cyril279/keyboards/documentation/pg1353.jpg

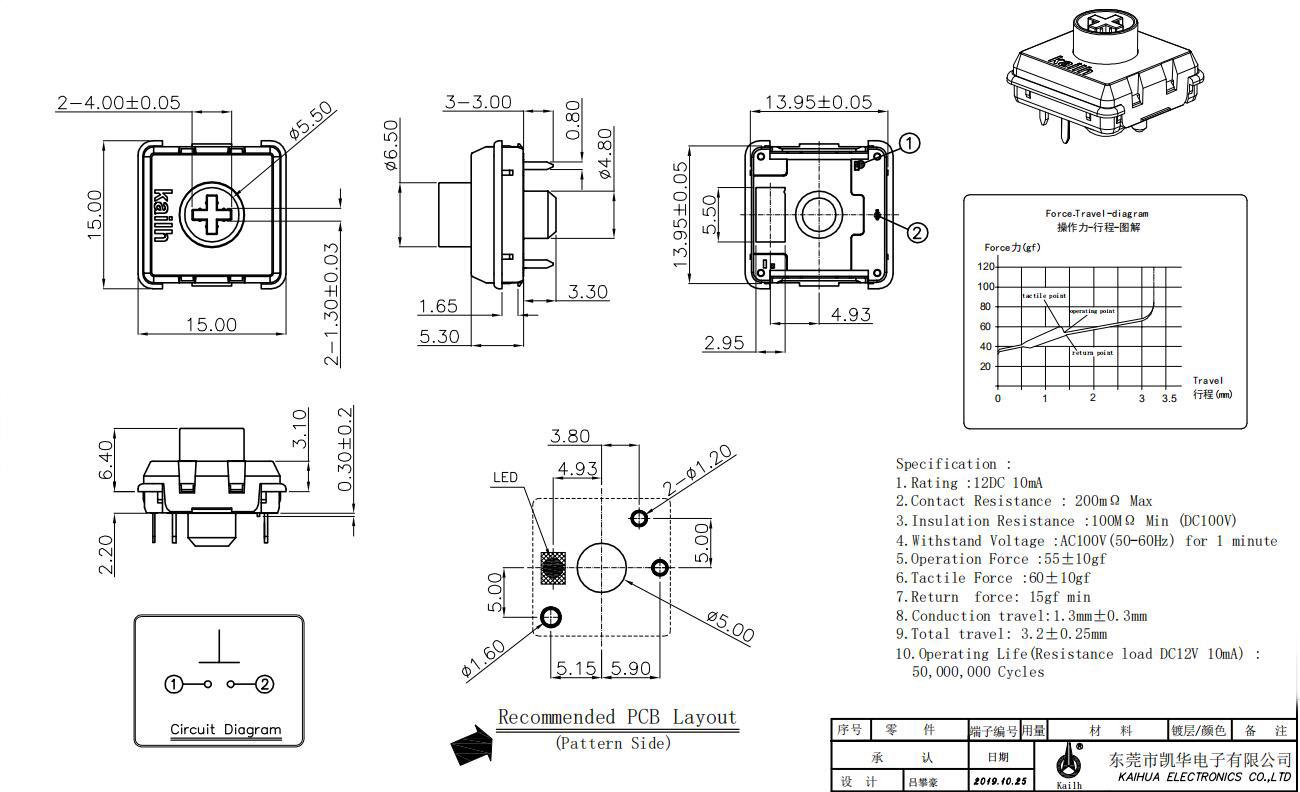
documentation/pg1353.jpg
