cyril279/keyboards/revlp/39_1350/documentation/pg1350_socket.jpg

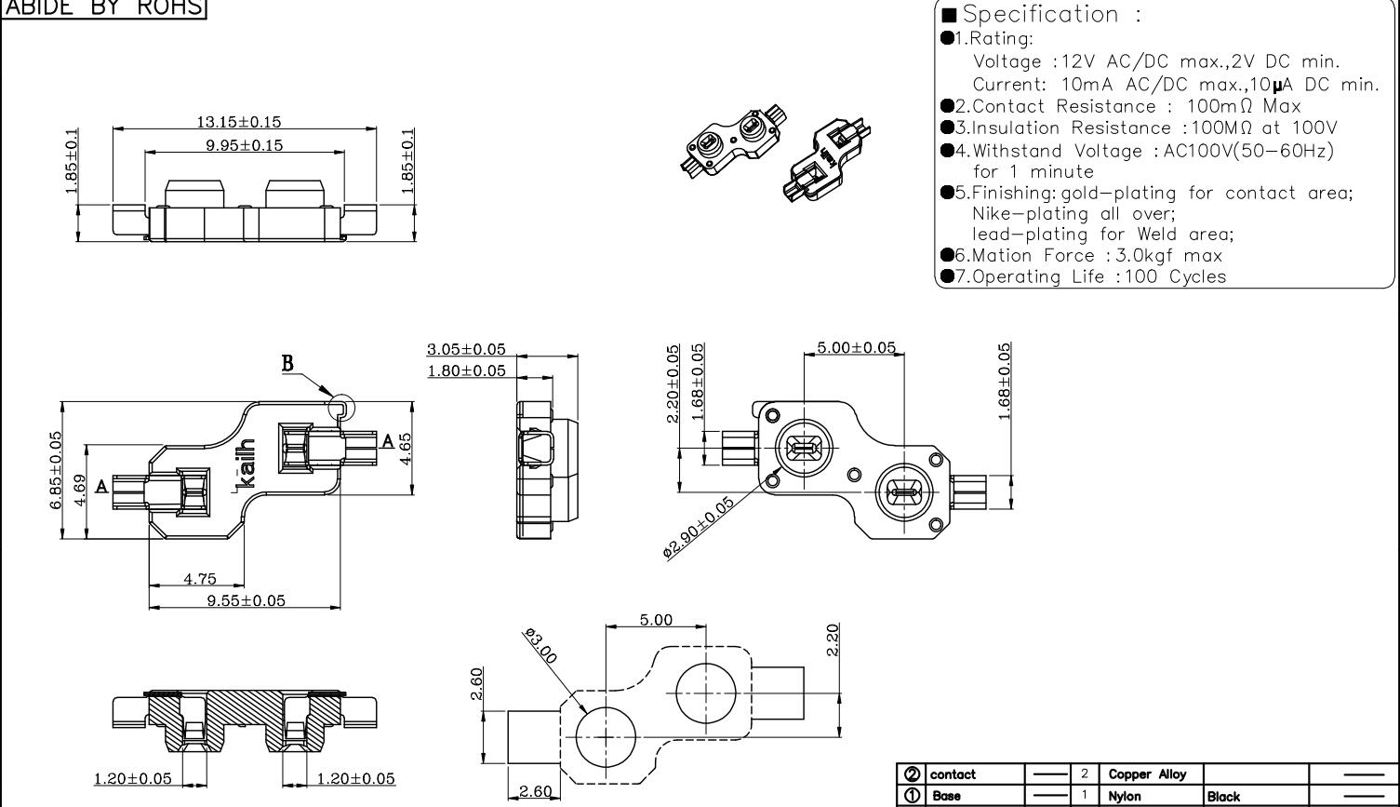
revlp/39_1350/documentation/pg1350_socket.jpg
