cyril279/keyboards/revlp/39_1350/documentation/pg1350_switch_alt.jpg

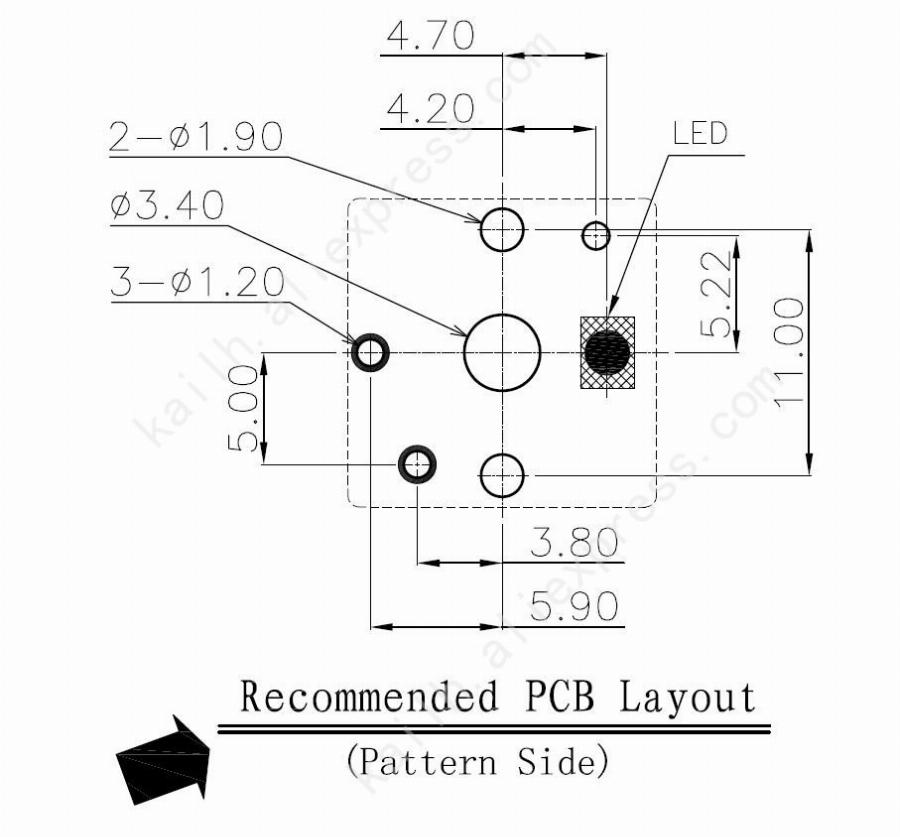
revlp/39_1350/documentation/pg1350_switch_alt.jpg
