cyril279/keyboards/revlp/41_1350/photos/PXL_20210316_154020069.jpg

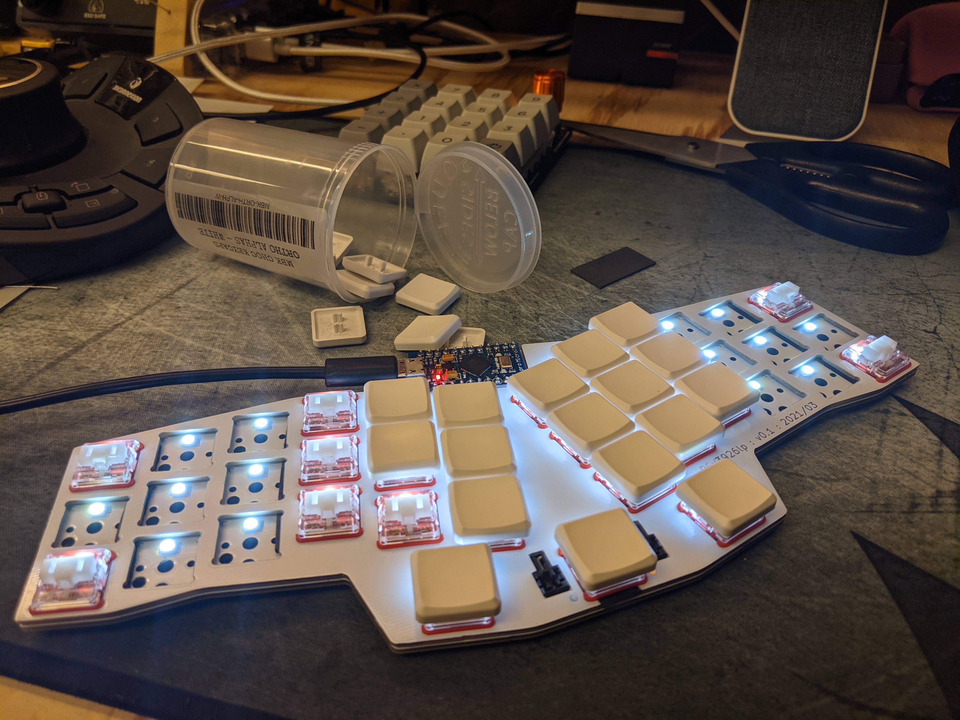
revlp/41_1350/photos/PXL_20210316_154020069.jpg
