cyril279/keyboards/revlp/41_1350/photos/PXL_20210531_201420430.jpg

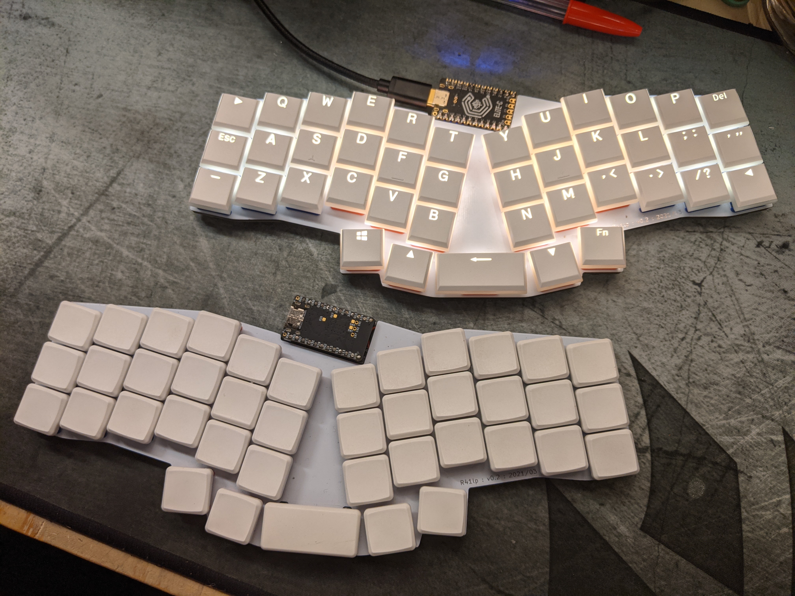
revlp/41_1350/photos/PXL_20210531_201420430.jpg
