cyril279/keyboards/revlp/41_1353/photos/PXL_20210806_121746867.jpg

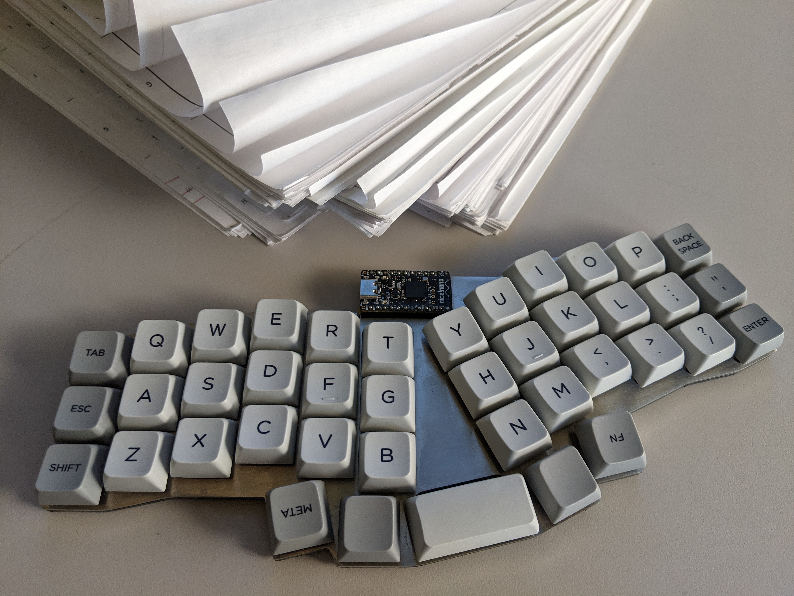
revlp/41_1353/photos/PXL_20210806_121746867.jpg
